samuelstroschein/Washer-Dryer-Interface/code client/include/pirSensor.h

# include <Arduino.h>
# include <Neotimer.h>


class PirSensor{

    private:
        int pin;
        // how many movements must be detected (to prevent false alarm)
        int THRESHOLD = 3;
        //how much time between detected motions get's reset
        Neotimer motionTimer = Neotimer(6000);

    public:

        int motionCounter = 0;

        PirSensor(int inputPin){
            this->pin = inputPin;
            pinMode(this->pin, INPUT);  
        }

        void measure(){
            if (digitalRead(pin) == HIGH){
                this->motionCounter = this->motionCounter + 1;
                //resume because function would restart timer every time otherwise
                motionTimer.start();
            }
            if (motionTimer.done()){
                this->motionCounter = 0;
                motionTimer.reset();
            } 
        }
        
        int detectsPerson(){
            if (motionCounter >= THRESHOLD){
                return true;
            }
            else{
                return false;
            }
        }
};
